open-tools/NodeMCU-i2c-Breakout-Board/images/IMG_0615.JPG

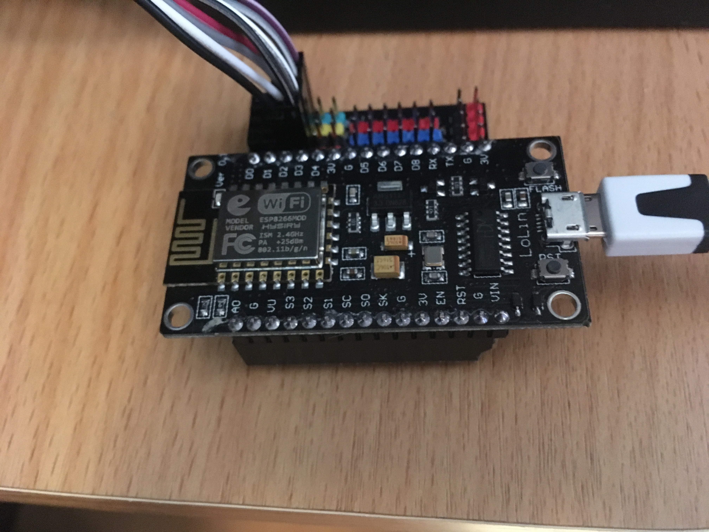
images/IMG_0615.JPG
